CentyLab/PicoPD/Documentation/doc7.png

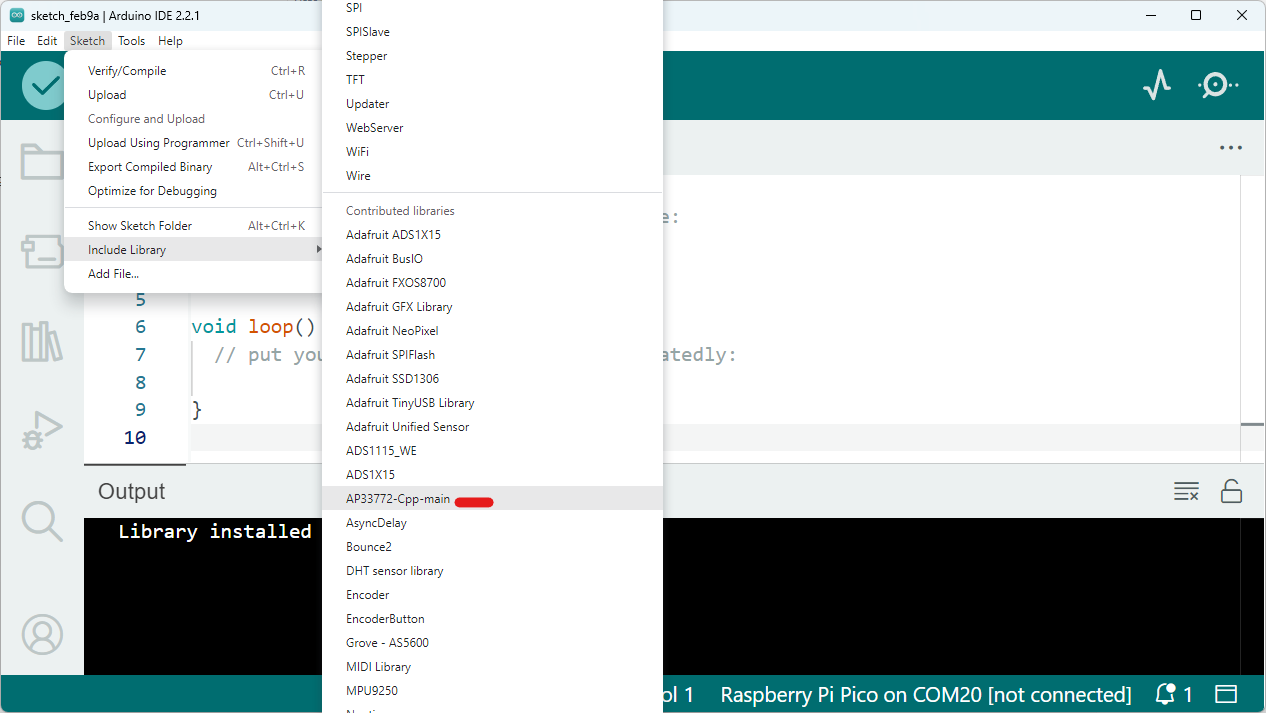
Documentation/doc7.png
